circool/IOT_Device/src/fan_actuator.h

// ============================================================================
// @file fan_actuator.h
// @brief Управление вентилятором с поддержкой ШИМ и стартового импульса
//
// Модуль реализует управление вентилятором с возможностью регулировки скорости
// методом широтно-импульсной модуляции (ШИМ). Обеспечивает стартовый импульс
// для надёжного запуска вентилятора при низких скоростях.
//
// @note Наследует базовый класс ActuatorBase, который отвечает за:
//       - включение/выключение
//       - контроль максимального времени работы (аварийное отключение)
//       - флаг аварийной остановки
//
// @note ШИМ настраивается через макросы:
//       - PWM_FREQUENCY — частота ШИМ (Гц)
//       - PWM_RESOLUTION — разрешение ШИМ (бит)
//       - PWM_STARTING — длительность стартового импульса (мс)
//
// @note Для ESP8266 используется аналоговый ШИМ через analogWrite(),
//       для ESP32 — аппаратный ШИМ через LEDC.
// ============================================================================

#ifndef FAN_ACTUATOR_H
#define FAN_ACTUATOR_H

#include "actuator_base.h"
#include "config.h"

/**
 * @class FanActuator
 * @brief Управление вентилятором с ШИМ и стартовым импульсом
 *
 * Расширяет возможности ActuatorBase:
 * - Регулировка скорости вращения от 0% до 100% (через ШИМ)
 * - Стартовый импульс на 100% мощности для раскрутки пропеллера
 * - Плавное переключение на целевую скорость после старта
 *
 * @note Вентилятор не может стартовать на низкой скорости — требуется
 *       стартовый импульс. При вызове set(true) с _currentSpeed < 100%,
 *       сначала подаётся 100% на PWM_STARTING мс, затем целевая скорость.
 *
 * @note При выключении (set(false)) система выходит из ШИМ-режима,
 *       пин переводится в дискретный режим.
 *
 * @note Адаптивный режим не входит в обязанности актуатора —
 *       это логика оркестратора (main.cpp).
 */
class FanActuator : public ActuatorBase {
 public:
  /**
   * @brief Конструктор вентилятора
   *
   * Инициализирует внутренние переменные:
   * - _currentSpeed = 0 (выключен)
   * - _pwmActive = false
   * - _startingPulseActive = false
   */
  FanActuator();

  /**
   * @brief Инициализация вентилятора
   *
   * Настраивает ШИМ (ESP32: ledcSetup, ESP8266: analogWriteFreq),
   * вызывает базовую инициализацию ActuatorBase, которая:
   * - устанавливает пин в режим OUTPUT
   * - применяет начальное состояние (bootState)
   *
   * @param pin          Номер GPIO для управления реле

   * @param bootState    Состояние при старте (true = включён)
   * @param defaultSpeed Скорость по умолчанию (0-100%)
   * @param maxOnTime    Максимальное время непрерывной работы (сек)
   *
   * @note Скорость по умолчанию используется при старте и восстанавливается
   *       после выключения. При ручной команде скорость сохраняется.
   */
  void init(uint8_t pin,
            bool bootState,
            uint16_t defaultSpeed,
            uint32_t maxOnTime);

  /**
   * @brief Установить скорость вращения
   *
   * @param percent Скорость в процентах (0-100)
   * @param manual  true — ручная команда (логируется как manual),
   *                false — автоматическая (из адаптивного режима)
   *
   * @note Если вентилятор включён и нет активного стартового импульса,
   *       скорость применяется немедленно через applySpeed().
   * @note Если вентилятор выключен, скорость сохраняется и будет применена
   *       при следующем включении (после стартового импульса).
   */
  void setSpeed(int percent, bool manual = true);

  /**
   * @brief Получить текущую скорость
   * @return Скорость в процентах (0-100)
   */
  int getSpeed() const;

  /**
   * @brief Периодический вызов в loop()
   *
   * Выполняет:
   * 1. Если активен стартовый импульс — по истечении PWM_STARTING мс
   *    переключается на целевую скорость.
   * 2. Вызывает ActuatorBase::update() для проверки maxOnTime.
   *
   * @note Стартовый импульс имеет приоритет над проверкой maxOnTime.
   */
  void update() override;

 protected:
  /**
   * @brief Обработка физического включения/выключения
   *
   * Реализация чисто виртуального метода ActuatorBase::onSetPhysical().
   *
   * @param on true — включить, false — выключить
   *
   * @note При включении (on = true):
   *       - Если скорость < 100% и > 0% — запускается стартовый импульс
   *         (applySpeed(100) временно)
   *       - Иначе — применяется целевая скорость
   * @note При выключении (on = false):
   *       - applySpeed(0) (выключить ШИМ, установить пин в !ACTIVE_LEVEL)
   *       - Сбрасывается флаг стартового импульса
   */
  void onSetPhysical(bool on) override;

 private:
  /**
   * @brief Применить скорость к физическому пину
   *
   * @param percent Скорость в процентах (0-100)
   *
   * @note Логика:
   *       - 0%: disablePWM(), digitalWrite(off)
   *       - 100%: disablePWM(), digitalWrite(on)
   *       - 1-99%: enablePWM(), установить ШИМ-значение
   *
   * @note Учитывает инверсию ACTIVE_LEVEL:
   *       - Если ACTIVE_LEVEL == LOW, ШИМ-значение инвертируется
   */
  void applySpeed(int percent);

  /**
   * @brief Включить ШИМ-режим на пине
   *
   * @note ESP32: ledcAttachPin()
   * @note ESP8266: не требуется (analogWrite() автоматически включает ШИМ)
   */
  void enablePWM();

  /**
   * @brief Выключить ШИМ-режим (вернуться к дискретному управлению)
   *
   * @note ESP32: ledcDetachPin()
   * @note ESP8266: analogWrite(pin, 1024) + delayMicroseconds(10) +
   * pinMode(OUTPUT) — это принудительно отключает ШИМ и возвращает пин в режим
   * GPIO.
   */
  void disablePWM();

  int _currentSpeed;          //!< Текущая скорость (0-100%)
  bool _pwmActive;            //!< Активен ли ШИМ в данный момент
  bool _startingPulseActive;  //!< Идёт ли стартовый импульс
  unsigned long
      _startingPulseStart;  //!< Время начала стартового импульса (millis)
};

#endif  // FAN_ACTUATOR_H
