circool/IOT_Device/src/led.cpp

#include "led.h"
#include <Arduino.h>
#include "logger.h"

#if STATUS_LED_PIN > 0

#ifndef LED_INVERTED
#ifdef ESP32
#define LED_INVERTED 0
#else
#define LED_INVERTED 1
#endif
#endif

static LedMode currentMode = LED_MODE_OFF;

void led_init() {
  pinMode(STATUS_LED_PIN, OUTPUT);
  digitalWrite(STATUS_LED_PIN, LED_INVERTED ? HIGH : LOW);
  LOG_INFO(CAT_LED, "Init pin %d (inverted=%d)", STATUS_LED_PIN, LED_INVERTED);
}

void led_setMode(LedMode mode) {
  if (currentMode != mode) {
    currentMode = mode;
    const char* names[] = {"OFF",
                           "NORMAL",
                           "NO WIFI (1 blink)",
                           "NO MQTT (2 blink)",
                           "AP MODE (3 blink)",
                           "EMERGENCY OFF (slow blink)"};
    LOG_INFO(CAT_LED, "Mode: %s", names[mode]);
  }
}

LedMode led_getMode() {
  return currentMode;
}

void led_update() {
  static bool lastState = false;
  unsigned long now = millis();
  bool shouldBeOn = false;
  // LED blink patterns use 1-second cycle (1000ms):
  // - Dit (short) = 100ms
  // - Dah (long)  = 300ms
  // - Gap between symbols = 100ms
  // Emergency pattern uses 800ms cycle for distinction
  switch (currentMode) {
    case LED_MODE_OFF:
      shouldBeOn = false;
      break;

    case LED_MODE_ON:
      shouldBeOn = true;
      break;

    case LED_MODE_MORZE_E:
      // 1 точка: █_______ (100 ON, 900 OFF)
      shouldBeOn = (now % 1000) < 100;
      break;

    case LED_MODE_MORZE_I:
      // 2 точки: █_█_____
      // 100 ON, 100 OFF, 100 ON, 700 OFF
      {
        unsigned long phase = now % 1000;
        shouldBeOn = (phase < 100) || (phase >= 200 && phase < 300);
      }
      break;

    case LED_MODE_MORZE_S:
      // 3 точки: █_█_█___
      // 100 ON, 100 OFF, 100 ON, 100 OFF, 100 ON, 500 OFF
      {
        unsigned long phase = now % 1000;
        shouldBeOn = (phase < 100) || (phase >= 200 && phase < 300) ||
                     (phase >= 400 && phase < 500);
      }
      break;

    case LED_SLOW_BLINK:
      // Режим аварийного отключения: 1 секунда горит, 1 секунда не горит
      // Период: 2000 мс
      {
        shouldBeOn = (now % 2000) < 1000;
        break;
      }
      break;
  }

  if (shouldBeOn != lastState) {
    lastState = shouldBeOn;
    digitalWrite(STATUS_LED_PIN, shouldBeOn ? (LED_INVERTED ? LOW : HIGH)
                                            : (LED_INVERTED ? HIGH : LOW));
  }
}

#endif
